jaredbotte/PIANO-PCB/Parts/796644-3/796644-3.step

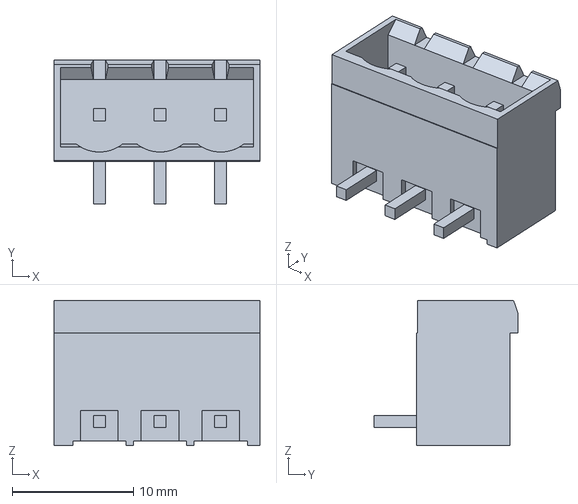
[picture p15: CAD file, 2021-09-28]
Parts/796644-3/796644-3.step
17.0 x 11.8 x 12.0 mm
